zzeneg/duet/images/curve2.jpg

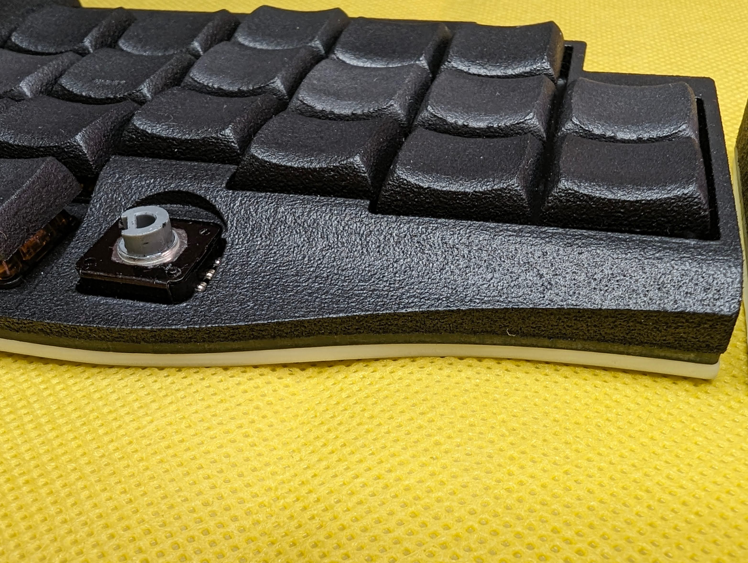
images/curve2.jpg
