zzeneg/duet/images/curve.jpg

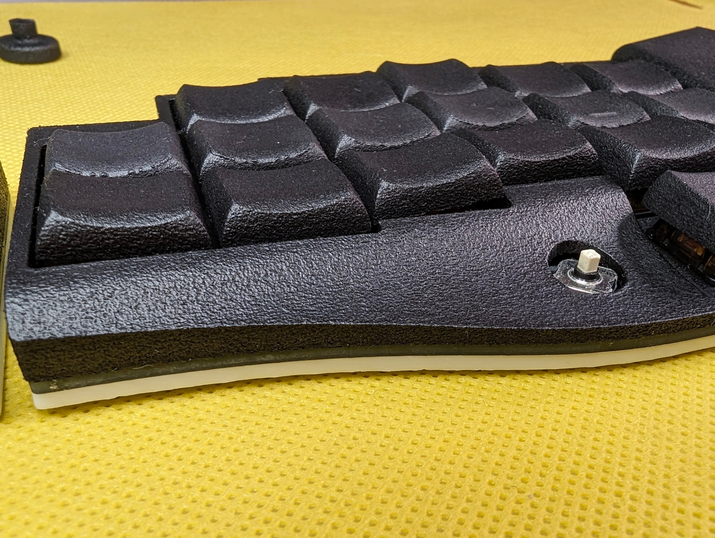
images/curve.jpg
