zzeneg/duet/images/usb.jpg

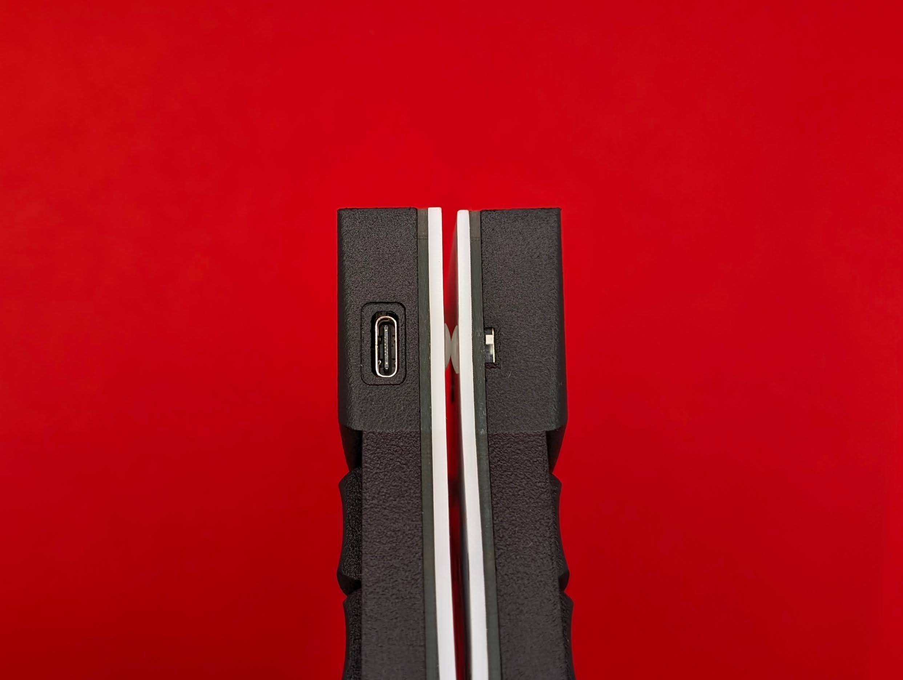
images/usb.jpg
