zzeneg/duet/guide/left-diode-2.jpg

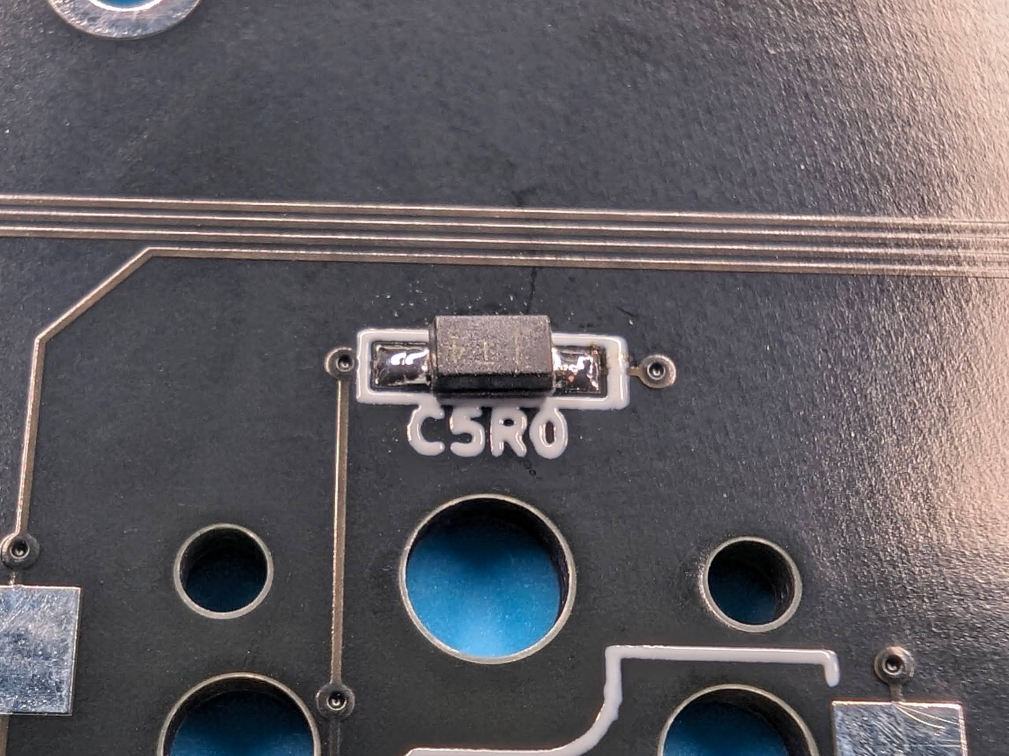
guide/left-diode-2.jpg
